astoeckel/wireless_doorbell/simulation/2022_05_13_opamp_schmitt_trigger_lowpass.asc

B1: bv; V=(white(2e6*time)/10)
C1: cap; 10µ
D1: schottky; 1N5819
L1: ind; 100µ; Rser=100
Q1: npn; BC547C
Q2: npn; BC547C
R1: res; 100k
R2: res; 10k
R3: res; 10k
R4: res; 100k
R5: res; 10k
R6: res; 10k
R7: res; 10k
U1: LT1006
U2: LT1006
V1: voltage; 12
V2: voltage; PULSE(0 12 0.1 0 0 1 0 1)
Named nets: 0
.tran 1s startup
