astoeckel/wireless_doorbell/simulation/2022_05_15_door_bell_power_supply.asc

C1: polcap; 1000µ; V=16 Irms=800m Rser=0.14 Lser=0
C2: polcap; 1000µ; V=16 Irms=800m Rser=0.14 Lser=0
C3: cap; 10n
C4: cap; 100µ
C6: cap; 10n
D1: schottky; 1N5819
D2: schottky; 1N5819
D3: schottky; 1N5819
D4: zener; 1N750
L2: ind; 100µ
M1: nmos; IRF7309N
M2: pmos; IRF7309P
R1: res; 100k
R2: res; 100k
R3: res; 10k
R4: res; 100k
R5: res; 100k
R6: res; 10
R7: res; 8
R9: res; 10
R11: res; 10k
R12: res; 10k
R13: res; 10k
U1: LT1006
U2: LT1006
V1: voltage; SINE(0 10 50 0 0 0 5)
Named nets: 0, fbck, vreg
.tran 10 startup
