astoeckel/wireless_doorbell/simulation/2022_07_30_door_bell_power_supply_2.asc

C1: cap; 100n
C4: polcap; 22µ; V=10 Irms=90m Rser=1.97249 Lser=1.22599n mfg="Würth Elektronik" pn="865060240001 WCAP-ASLL 4x5,5" type="Al electrolytic"
C5: polcap; 470µ; V=25 Irms=130m Rser=0.365423 Lser=5.51428n
C6: polcap; 470µ; V=25 Irms=130m Rser=0.365423 Lser=5.51428n
D1: diode; 1N4148
D2: diode; 1N4148
D3: diode; 1N4148
D4: TVSdiode; SMBJ24CA
D5: diode; 1N4148
D6: TVSdiode; SMBJ24CA
R1: res; 100
R2: res; 10k
R4: res; 10
R5: res; 6.8k
U1: LT1117-3.3
U3: CNY17-1
V1: voltage; SINE(0 8 50 0 0 0 0)
V2: voltage; SINE(0 9.8 50 0 0 0 25)
V3: voltage; SINE(0 8 50 0 0 0 25)
V4: voltage; PULSE(0 100 0.1 0 0 0.0001 0.002 1)
Named nets: 0, dgnd, dvcc, dsense, ge, ws, sw
.tran 1 startup
1W Resistor
DC/DC buck converter
Reichelt "1,5KE 36CA"
